mangel890/virtualcockpit/images/ard1.jpg

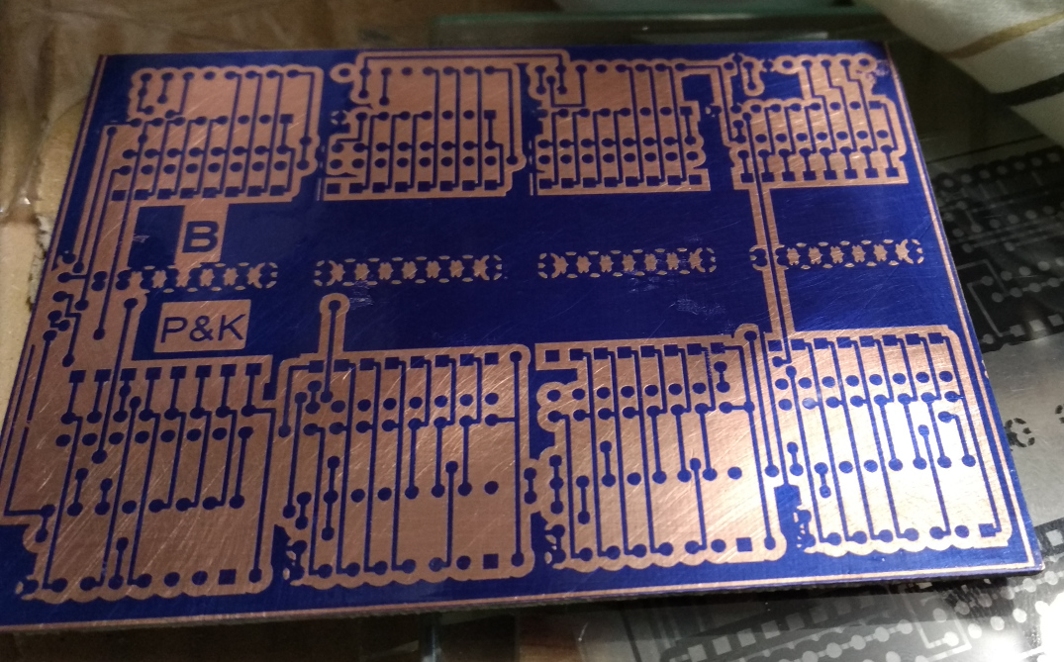
images/ard1.jpg
