mangel890/virtualcockpit/images/mcp2.jpg

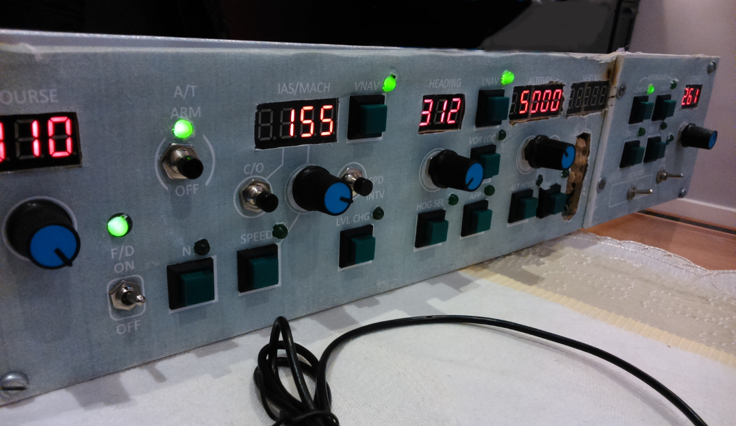
images/mcp2.jpg
